sjgray/RTC-Links/RTC-Link2/rtclink2-bot.jpg

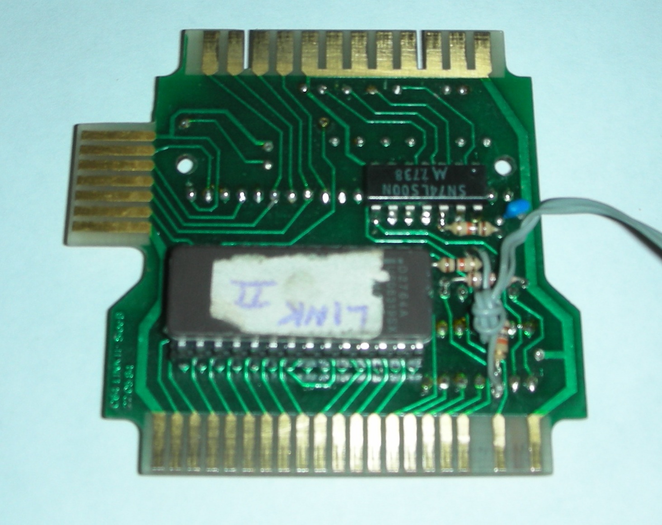
RTC-Link2/rtclink2-bot.jpg
