sjgray/RTC-Links/RTC-Link2/rtclink2-pcb-b-reversed.jpg

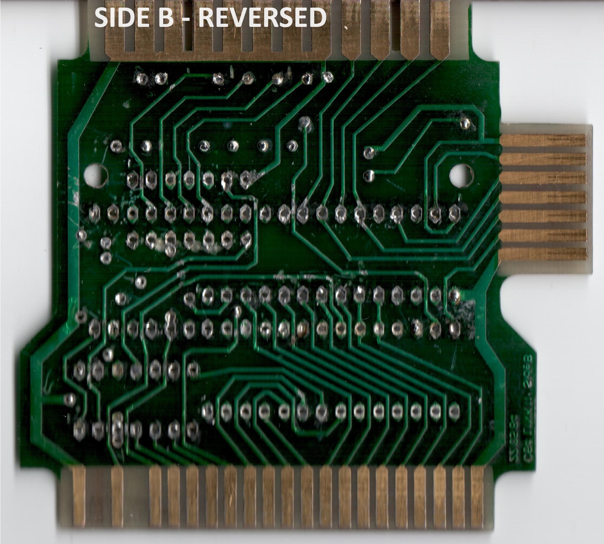
RTC-Link2/rtclink2-pcb-b-reversed.jpg
