sjgray/RTC-Links/RTC-Link2/rtclink2-pcb-b.jpg

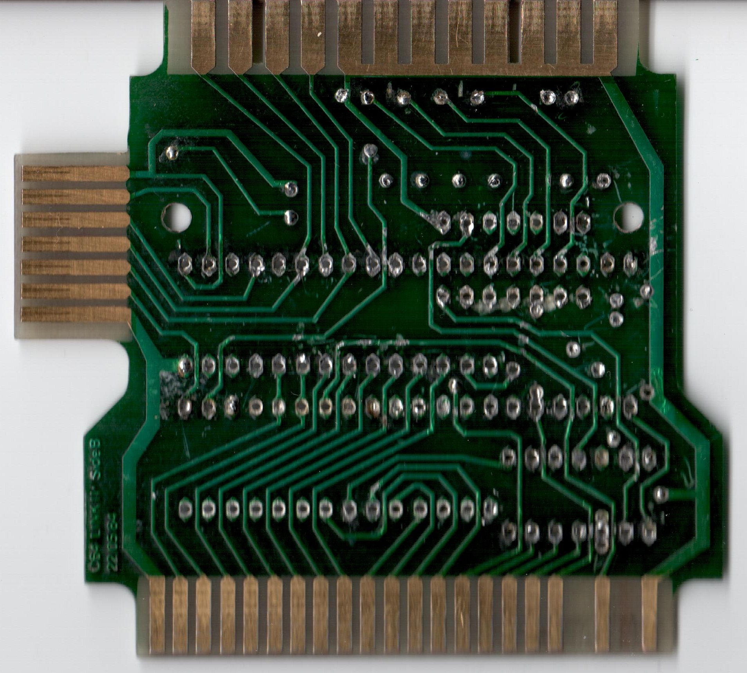
RTC-Link2/rtclink2-pcb-b.jpg
