sjgray/RTC-Links/RTC-Link2/RTC-Link2.kicad_sch

## KiCad design RTC-Link2/RTC-Link2.kicad_sch (2025-04-04)

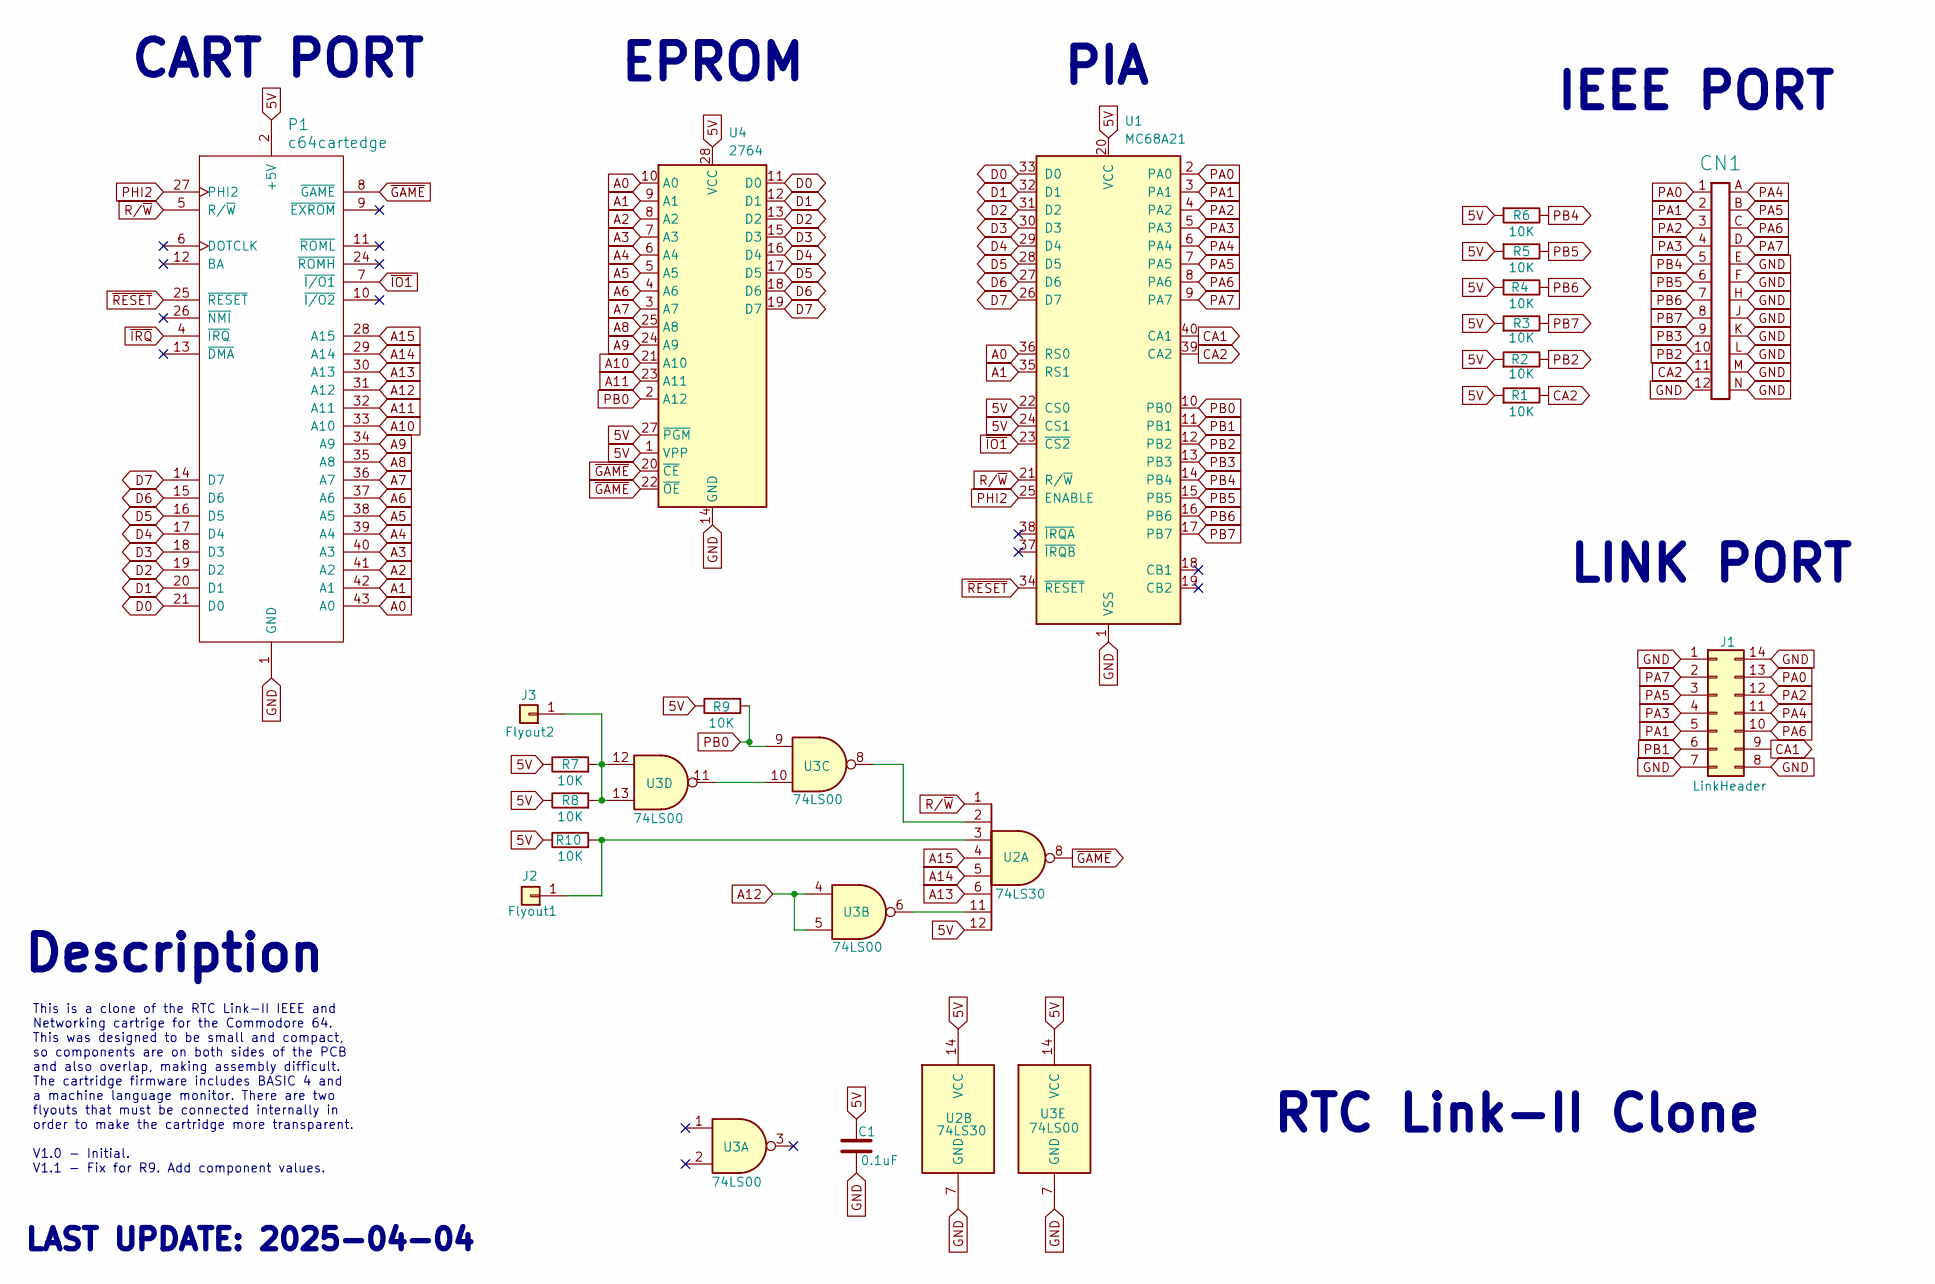
[picture p13: schematic RTC-Link2.kicad_sch]

Parts:
C1: 0.1uF; C_Disc_D3.0mm_W2.0mm_P2.50mm
CN1: EDGE_CON_02x12; petieee
J1: LinkHeader; EDGE_CON_14p
J2: Flyout1; PinHeader_1x01_P2.54mm_Vertical
J3: Flyout2; PinHeader_1x01_P2.54mm_Vertical
P1: c64cartedge
R1, R2, R3, R4, R5, R6, R7, R8, R9, R10: 10K; R_Axial_DIN0204_L3.6mm_D1.6mm_P7.62mm_Horizontal
U1: MC68A21; DIP-40_W15.24mm
U2: 74LS30; DIP-14_W7.62mm_LongPads
U3: 74LS00; DIP-14_W7.62mm_LongPads
U4: 2764; DIP-28_W15.24mm

Connections:
5V: C1.1, P1.2 (+5V), P1.3 (+5V), R1.2, R2.2, R3.2, R4.2, R5.2, R6.2, R7.1, R8.1, R9.1, R10.1, U1.20 (VCC), U1.22 (CS0), U1.24 (CS1), U2.12, U2.14 (VCC), U3.14 (VCC), U4.1 (VPP), U4.27 (~PGM), U4.28 (VCC)
A0: P1.43 (A0), U1.36 (RS0), U4.10 (A0)
A1: P1.42 (A1), U1.35 (RS1), U4.9 (A1)
A2: P1.41 (A2), U4.8 (A2)
A3: P1.40 (A3), U4.7 (A3)
A4: P1.39 (A4), U4.6 (A4)
A5: P1.38 (A5), U4.5 (A5)
A6: P1.37 (A6), U4.4 (A6)
A7: P1.36 (A7), U4.3 (A7)
A8: P1.35 (A8), U4.25 (A8)
A9: P1.34 (A9), U4.24 (A9)
A10: P1.33 (A10), U4.21 (A10)
A11: P1.32 (A11), U4.23 (A11)
A12: P1.31 (A12), U3.4, U3.5
A13: P1.30 (A13), U2.6
A14: P1.29 (A14), U2.5
A15: P1.28 (A15), U2.4
CA1: J1.9, U1.40 (CA1)
CA2: CN1.11, R1.1, U1.39 (CA2)
D0: P1.21 (D0), U1.33 (D0), U4.11 (D0)
D1: P1.20 (D1), U1.32 (D1), U4.12 (D1)
D2: P1.19 (D2), U1.31 (D2), U4.13 (D2)
D3: P1.18 (D3), U1.30 (D3), U4.15 (D3)
D4: P1.17 (D4), U1.29 (D4), U4.16 (D4)
D5: P1.16 (D5), U1.28 (D5), U4.17 (D5)
D6: P1.15 (D6), U1.27 (D6), U4.18 (D6)
D7: P1.14 (D7), U1.26 (D7), U4.19 (D7)
GND: C1.2, CN1.12, CN1.E, CN1.F, CN1.H, CN1.J, CN1.K, CN1.L, CN1.M, CN1.N, J1.1, J1.7, J1.8, J1.14, P1.1 (GND), P1.22 (GND), P1.23 (GND), P1.44 (GND), U1.1 (VSS), U2.7 (GND), U3.7 (GND), U4.14 (GND)
unnamed: J2.1, R10.2, U2.3
unnamed: J3.1, R7.2, R8.2, U3.12, U3.13
unnamed: U2.2, U3.8
unnamed: U2.11, U3.6
unnamed: U3.10, U3.11
PA0: CN1.1, J1.13, U1.2 (PA0)
PA1: CN1.2, J1.5, U1.3 (PA1)
PA2: CN1.3, J1.12, U1.4 (PA2)
PA3: CN1.4, J1.4, U1.5 (PA3)
PA4: CN1.A, J1.11, U1.6 (PA4)
PA5: CN1.B, J1.3, U1.7 (PA5)
PA6: CN1.C, J1.10, U1.8 (PA6)
PA7: CN1.D, J1.2, U1.9 (PA7)
PB0: R9.2, U1.10 (PB0), U3.9, U4.2 (A12)
PB1: J1.6, U1.11 (PB1)
PB2: CN1.10, R2.1, U1.12 (PB2)
PB3: CN1.9, U1.13 (PB3)
PB4: CN1.5, R6.1, U1.14 (PB4)
PB5: CN1.6, R5.1, U1.15 (PB5)
PB6: CN1.7, R4.1, U1.16 (PB6)
PB7: CN1.8, R3.1, U1.17 (PB7)
PHI2: P1.27 (PHI2), U1.25 (ENABLE)
R/~W: P1.5 (R/~W), U1.21 (R/~W), U2.1
~GAME: P1.8 (~GAME), U2.8, U4.20 (~CE), U4.22 (~OE)
~IO1: P1.7 (~I/O1), U1.23 (~CS2)
~IRQ: P1.4 (~IRQ)
~RESET: P1.25 (~RESET), U1.34 (~RESET)

Notes on the sheet:
IEEE PORT
Description
EPROM
LAST UPDATE: 2025-04-04
PIA
This is a clone of the RTC Link-II IEEE and Networking cartrige for the Commodore 64. This was designed to be small and compact, so components are on both sides of the PCB and also overlap, making assembly difficult. The cartridge firmware includes BASIC 4 and a machine language monitor. There are 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
CART PORT
RTC Link-II Clone
LINK PORT
